aryansaini-71/speakfix/Documents/H1.png

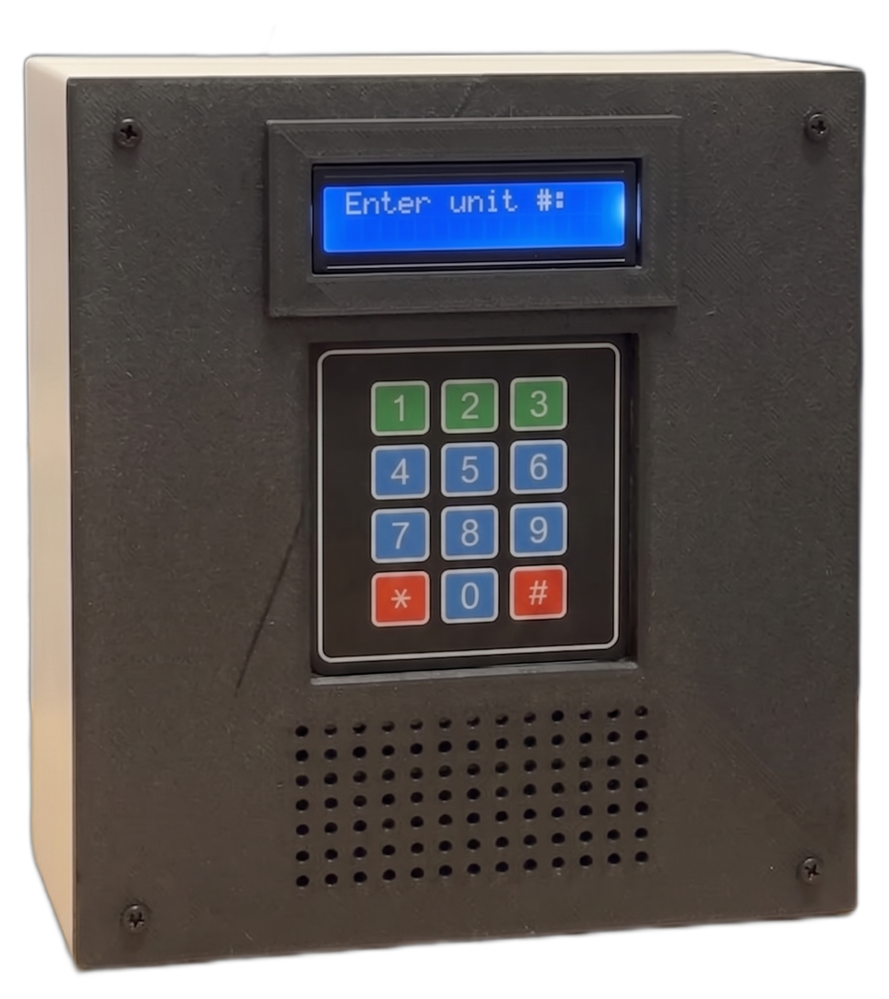
Documents/H1.png
