aryansaini-71/speakfix/Documents/H2.jpeg

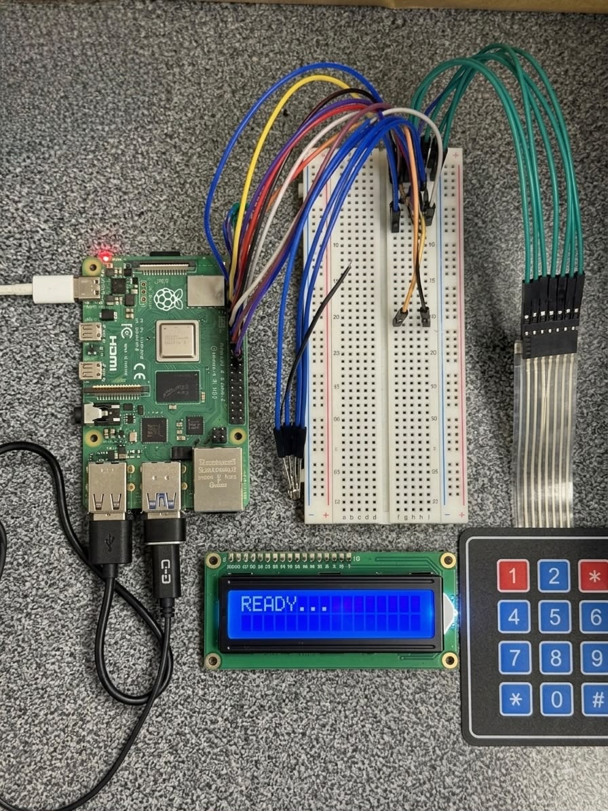
Documents/H2.jpeg
