aryansaini-71/speakfix/Documents/H3.jpeg

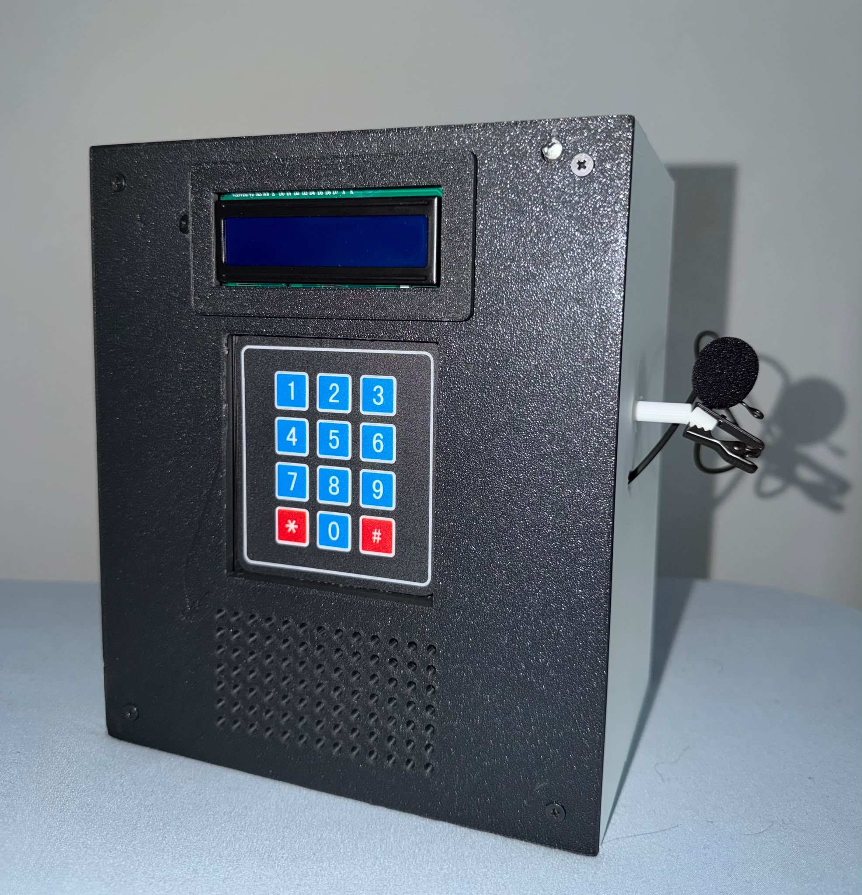
Documents/H3.jpeg
