aryansaini-71/speakfix/Documents/S1.png

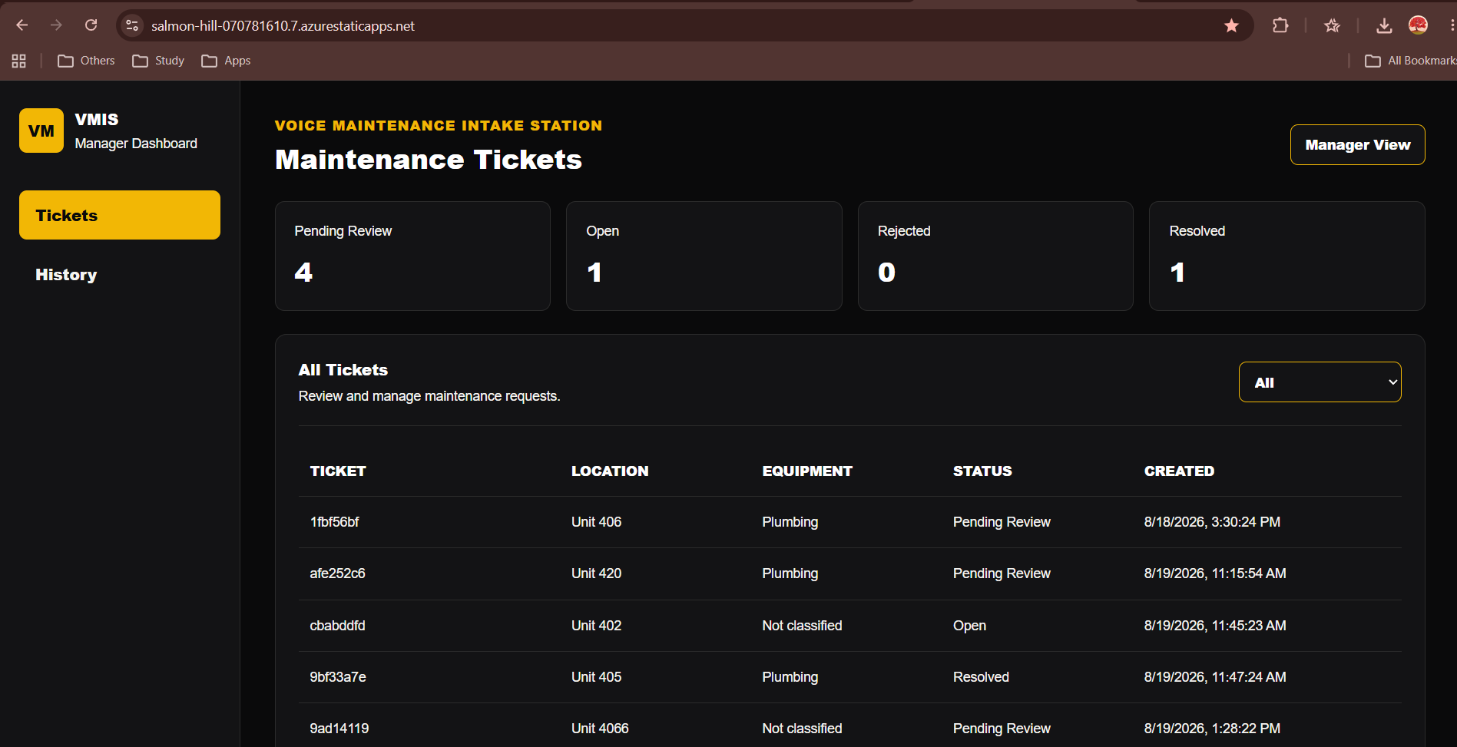
Documents/S1.png
