aryansaini-71/speakfix/Documents/S3.png

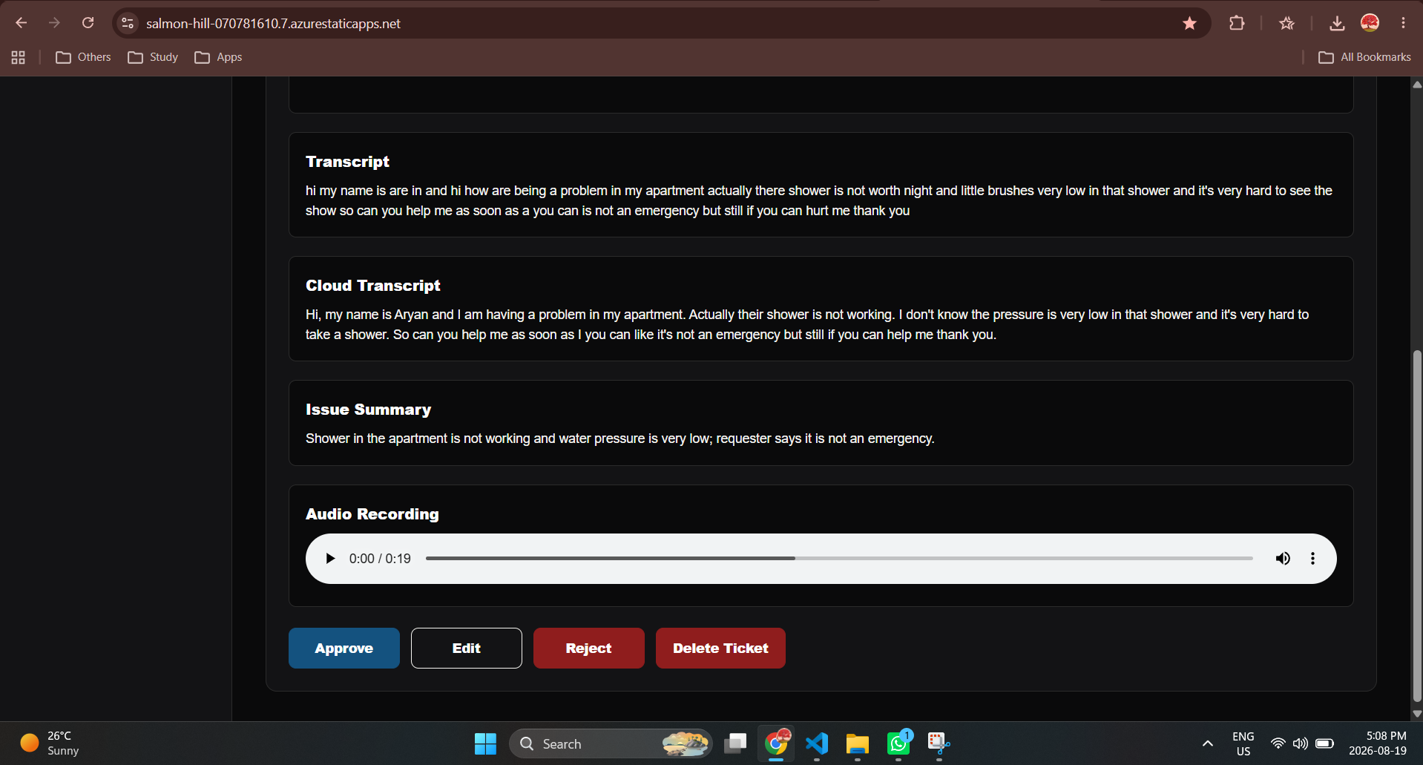
Documents/S3.png
