aryansaini-71/speakfix/Documents/S4.png

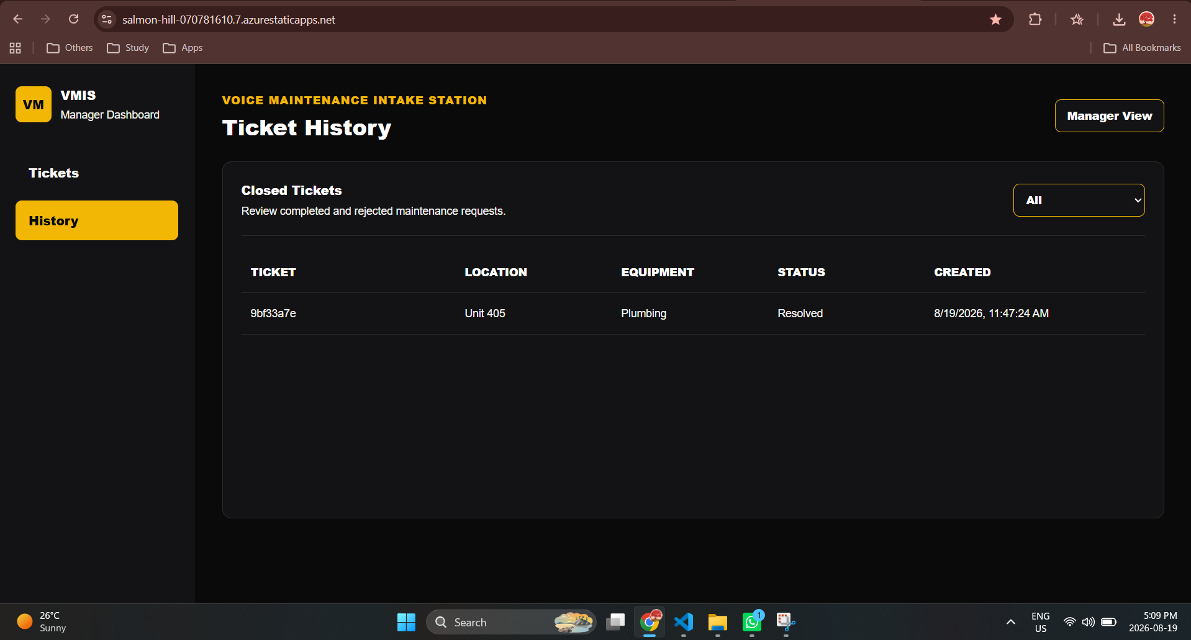
Documents/S4.png
